undotcom/home-assistant-audio-speaker-v2/images/compact_home_assistant_speaker_front.jpg

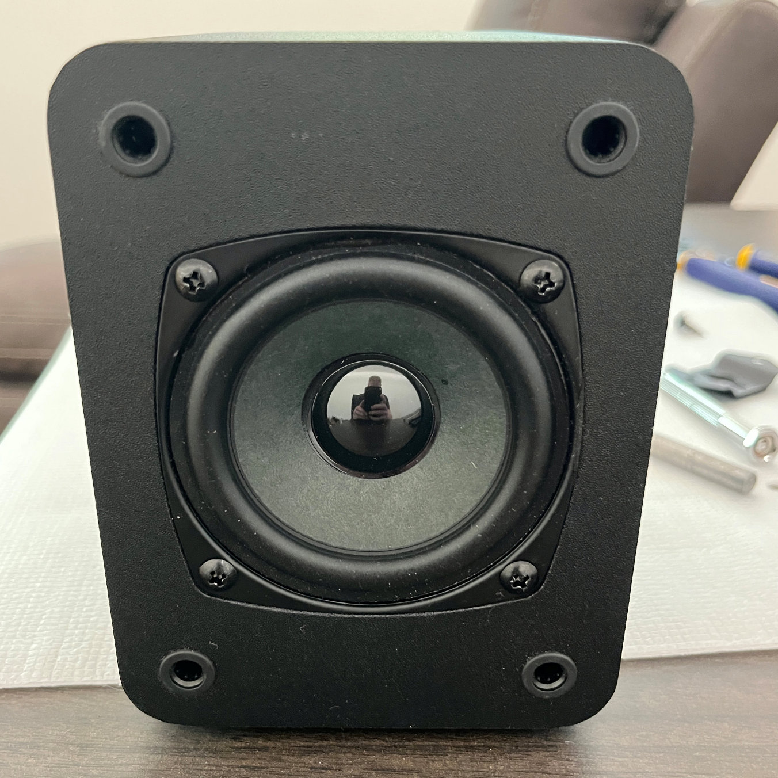
images/compact_home_assistant_speaker_front.jpg
